Crayon-PK/Waste-Classification-Project/picture/IMG20260606160427.jpg

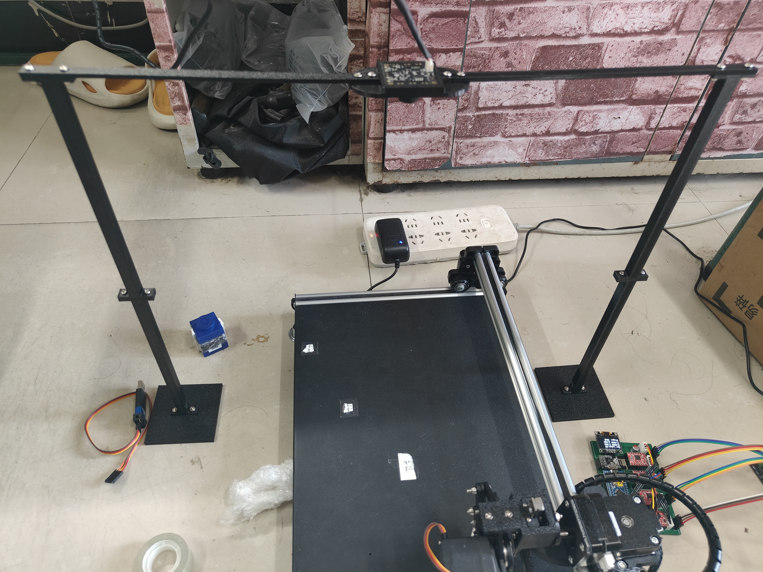
picture/IMG20260606160427.jpg
