Crayon-PK/Waste-Classification-Project/Firmware/BSP/Servo.c

#include "stm32f10x.h"                  // Device header

/**
  * 函    数：舵机初始化
  * 参    数：无
  * 返 回 值：无
  */
void Servo_Init(void)
{
	/* 开启时钟 */
	RCC_APB2PeriphClockCmd(RCC_APB2Periph_TIM1 | RCC_APB2Periph_GPIOA, ENABLE);

	/* GPIO初始化 */
	GPIO_InitTypeDef GPIO_InitStructure;
	GPIO_InitStructure.GPIO_Pin = GPIO_Pin_8;               // PA8
	GPIO_InitStructure.GPIO_Mode = GPIO_Mode_AF_PP;         // 复用推挽
	GPIO_InitStructure.GPIO_Speed = GPIO_Speed_50MHz;
	GPIO_Init(GPIOA, &GPIO_InitStructure);

	/* 时基单元初始化 */
	TIM_TimeBaseInitTypeDef TIM_TimeBaseInitStructure;
	TIM_TimeBaseInitStructure.TIM_Period = 20000 - 1;       // ARR
	TIM_TimeBaseInitStructure.TIM_Prescaler = 72 - 1;       // PSC
	TIM_TimeBaseInitStructure.TIM_ClockDivision = TIM_CKD_DIV1;
	TIM_TimeBaseInitStructure.TIM_CounterMode = TIM_CounterMode_Up;
	TIM_TimeBaseInitStructure.TIM_RepetitionCounter = 0;
	TIM_TimeBaseInit(TIM1, &TIM_TimeBaseInitStructure);

	/* 输出比较初始化 */
	TIM_OCInitTypeDef TIM_OCInitStructure;
	TIM_OCStructInit(&TIM_OCInitStructure);
	TIM_OCInitStructure.TIM_OCMode = TIM_OCMode_PWM1;
	TIM_OCInitStructure.TIM_OutputState = TIM_OutputState_Enable;
	TIM_OCInitStructure.TIM_OCPolarity = TIM_OCPolarity_High;
	TIM_OCInitStructure.TIM_Pulse = 0;                     // 初始CCR
	TIM_OC1Init(TIM1, &TIM_OCInitStructure);
	TIM_OC1PreloadConfig(TIM1, TIM_OCPreload_Enable);

	/* 使能 TIM1 输出PWM */
	TIM_CtrlPWMOutputs(TIM1, ENABLE);      // 高级定时器必须使能主输出
	TIM_Cmd(TIM1, ENABLE);
}

/**
  * 函    数：舵机设置角度
  * 参    数：Angle 要设置的舵机角度，范围：0~180
  * 返 回 值：无
  */
void Servo_SetAngle(float Angle)
{
	TIM_SetCompare1(TIM1,Angle / 180 * 2000 + 500);	//设置占空比
												//将角度线性变换，对应到舵机要求的占空比范围上
}
