Crayon-PK/Waste-Classification-Project/Firmware/BSP/NRF24L01.c

#include "stm32f10x.h"
#include "NRF24L01_Define.h"
#include <stddef.h>

/*---------------- 引脚定义 ----------------*/
#define NRF_CE   GPIO_Pin_1
#define NRF_CSN  GPIO_Pin_9
#define NRF_SCK  GPIO_Pin_10
#define NRF_MOSI GPIO_Pin_11
#define NRF_MISO GPIO_Pin_12
#define NRF_IRQ  GPIO_Pin_15

/*发送部分*/
uint8_t NRF24L01_TxAddress[5] = {0xAA, 0xBB, 0xCC, 0xDD, 0xEE};		//发送地址，固定5字节
#define NRF24L01_TX_PACKET_WIDTH		32							//发送数据包宽度，范围：1~32字节
uint8_t NRF24L01_TxPacket[NRF24L01_TX_PACKET_WIDTH];				//发送数据包

/*接收部分*/
uint8_t NRF24L01_RxAddress[5] = {0x11, 0x22, 0x33, 0x44, 0x55};		//接收通道0地址，固定5字节
#define NRF24L01_RX_PACKET_WIDTH		32							//接收通道0数据包宽度，范围：1~32字节
uint8_t NRF24L01_RxPacket[NRF24L01_RX_PACKET_WIDTH];				//接收数据包

typedef void (*NRF24L01_Callback_t)(uint8_t event);// event = 1: 接收完成, 2: 发送完成, 3: 达到最大重发次数
static NRF24L01_Callback_t driver_callback = NULL;

void NRF24L01_RegisterCallback(NRF24L01_Callback_t cb)
{ 
	driver_callback = cb;
}


void NRF24L01_W_CE(uint8_t BitValue){ GPIO_WriteBit(GPIOA, NRF_CE, (BitAction)BitValue); }
void NRF24L01_W_CSN(uint8_t BitValue){ GPIO_WriteBit(GPIOA, NRF_CSN, (BitAction)BitValue); }
void NRF24L01_W_SCK(uint8_t BitValue){ GPIO_WriteBit(GPIOA, NRF_SCK, (BitAction)BitValue); }
void NRF24L01_W_MOSI(uint8_t BitValue){ GPIO_WriteBit(GPIOA, NRF_MOSI, (BitAction)BitValue); }
uint8_t NRF24L01_R_MISO(void){ return GPIO_ReadInputDataBit(GPIOA, NRF_MISO); }

/**
  * 函    数：NRF24L01引脚初始化
  * 参    数：无
  * 返 回 值：无
  * 说    明：当上层函数需要初始化时，此函数会被调用
  *           用户需要将CSN、CE、MISO、SCK引脚初始化为推挽输出模式，MISO引脚初始化为上拉输入模式
  */
void NRF24L01_GPIO_Init(void)
{
	/*开启GPIO时钟*/
	RCC_APB2PeriphClockCmd(RCC_APB2Periph_GPIOA, ENABLE);
	GPIO_InitTypeDef GPIO_InitStructure;

	/* CE, CSN, SCK, MOSI 输出 */
	GPIO_InitStructure.GPIO_Mode = GPIO_Mode_Out_PP;
	GPIO_InitStructure.GPIO_Pin = NRF_CE | NRF_CSN | NRF_SCK | NRF_MOSI;
	GPIO_InitStructure.GPIO_Speed = GPIO_Speed_50MHz;
	GPIO_Init(GPIOA, &GPIO_InitStructure);

	/* MISO 输入上拉 */
	GPIO_InitStructure.GPIO_Mode = GPIO_Mode_IPU;
	GPIO_InitStructure.GPIO_Pin = NRF_MISO;
	GPIO_Init(GPIOA, &GPIO_InitStructure);
	
	/*置引脚初始化后的默认电平*/
	NRF24L01_W_CE(0);		//CE默认为0，退出收发模式
	NRF24L01_W_CSN(1);		//CSN默认为1，不选中从机
	NRF24L01_W_SCK(0);		//SCK默认为0，对应SPI模式0
	NRF24L01_W_MOSI(0);		//MOSI默认电平随意，1和0均可
}

void NRF24L01_IRQ_Init(void)
{
	GPIO_InitTypeDef GPIO_InitStructure;
	EXTI_InitTypeDef EXTI_InitStructure;
	NVIC_InitTypeDef NVIC_InitStructure;

	// 配置 PA15 为输入上拉
	RCC_APB2PeriphClockCmd(RCC_APB2Periph_GPIOA, ENABLE);
	GPIO_InitStructure.GPIO_Pin = NRF_IRQ;
	GPIO_InitStructure.GPIO_Mode = GPIO_Mode_IPU;  // 上拉输入
	GPIO_Init(GPIOA, &GPIO_InitStructure);

	// 配置外部中断线
	RCC_APB2PeriphClockCmd(RCC_APB2Periph_AFIO, ENABLE);
	GPIO_EXTILineConfig(GPIO_PortSourceGPIOA, GPIO_PinSource15);

	EXTI_InitStructure.EXTI_Line = EXTI_Line15;
	EXTI_InitStructure.EXTI_Mode = EXTI_Mode_Interrupt;
	EXTI_InitStructure.EXTI_Trigger = EXTI_Trigger_Falling;  // IRQ 低电平触发
	EXTI_InitStructure.EXTI_LineCmd = ENABLE;
	EXTI_Init(&EXTI_InitStructure);

	// 配置中断优先级
	NVIC_InitStructure.NVIC_IRQChannel = EXTI15_10_IRQn;
	NVIC_InitStructure.NVIC_IRQChannelPreemptionPriority = 11;
	NVIC_InitStructure.NVIC_IRQChannelSubPriority = 0;
	NVIC_InitStructure.NVIC_IRQChannelCmd = ENABLE;
	NVIC_Init(&NVIC_InitStructure);
}

/*********************引脚配置*/


/*通信协议*********************/

/**
  * 函    数：SPI交换一个字节
  * 参    数：Byte 要发送的一个字节数据，范围：0x00~0xFF
  * 返 回 值：接收得到的一个字节数据，范围：0x00~0xFF
  */
uint8_t NRF24L01_SPI_SwapByte(uint8_t Byte)
{
    uint8_t i;
    for (i = 0; i < 8; i++)
    {
        if (Byte & 0x80) NRF24L01_W_MOSI(1);
        else NRF24L01_W_MOSI(0);
        Byte <<= 1;
        NRF24L01_W_SCK(1);
        if (NRF24L01_R_MISO()) Byte |= 0x01;
        NRF24L01_W_SCK(0);
    }
    return Byte;
}

/*********************通信协议*/


/*指令实现*********************/

/**
  * 函    数：NRF24L01读取寄存器（一个字节）
  * 参    数：RegAddress 指定寄存器地址，范围：0x00~0x1F
  * 返 回 值：指定寄存器的数据，范围：0x00~0xFF
  */
uint8_t NRF24L01_ReadReg(uint8_t RegAddress)
{
    uint8_t Data;
    NRF24L01_W_CSN(0);
    NRF24L01_SPI_SwapByte(NRF24L01_R_REGISTER | RegAddress);
    Data = NRF24L01_SPI_SwapByte(NRF24L01_NOP);
    NRF24L01_W_CSN(1);
    return Data;
}

/**
  * 函    数：NRF24L01读取寄存器（多个字节）
  * 参    数：RegAddress 指定寄存器的地址，范围：0x00~0x1F
  * 参    数：DataArray 读取得到的数据数组，输出参数
  * 参    数：Count 指定读取的数量，范围：0~5
  * 返 回 值：无
  */
void NRF24L01_ReadRegs(uint8_t RegAddress, uint8_t *DataArray, uint8_t Count)
{
    uint8_t i;
    NRF24L01_W_CSN(0);
    NRF24L01_SPI_SwapByte(NRF24L01_R_REGISTER | RegAddress);
    for (i = 0; i < Count; i++) DataArray[i] = NRF24L01_SPI_SwapByte(NRF24L01_NOP);
    NRF24L01_W_CSN(1);
}

/**
  * 函    数：NRF24L01写入寄存器（一个字节）
  * 参    数：RegAddress 指定寄存器地址，范围：0x00~0x1F
  * 参    数：Data 要写入的一个字节数据，范围：0x00~0xFF
  * 返 回 值：无
  */
void NRF24L01_WriteReg(uint8_t RegAddress, uint8_t Data)
{
    NRF24L01_W_CSN(0);
    NRF24L01_SPI_SwapByte(NRF24L01_W_REGISTER | RegAddress);
    NRF24L01_SPI_SwapByte(Data);
    NRF24L01_W_CSN(1);
}

/**
  * 函    数：NRF24L01写入寄存器（多个字节）
  * 参    数：RegAddress 指定寄存器地址，范围：0x00~0x1F
  * 参    数：DataArray 要写入的数据数组，输入参数
  * 参    数：Count 指定写入的数量，范围：0~5
  * 返 回 值：无
  */
void NRF24L01_WriteRegs(uint8_t RegAddress, uint8_t *DataArray, uint8_t Count)
{
    uint8_t i;
    NRF24L01_W_CSN(0);
    NRF24L01_SPI_SwapByte(NRF24L01_W_REGISTER | RegAddress);
    for (i = 0; i < Count; i++) NRF24L01_SPI_SwapByte(DataArray[i]);
    NRF24L01_W_CSN(1);
}

/**
  * 函    数：NRF24L01读取Rx有效载荷
  * 参    数：DataArray 读取得到的数据数组，输出参数
  * 参    数：Count 指定读取的数量，范围：0~32
  * 返 回 值：无
  */
void NRF24L01_ReadRxPayload(uint8_t *DataArray, uint8_t Count)
{
    uint8_t i;
    NRF24L01_W_CSN(0);
    NRF24L01_SPI_SwapByte(NRF24L01_R_RX_PAYLOAD);
    for (i = 0; i < Count; i++) DataArray[i] = NRF24L01_SPI_SwapByte(NRF24L01_NOP);
    NRF24L01_W_CSN(1);
}


/**
  * 函    数：NRF24L01写入Tx有效载荷
  * 参    数：DataArray 要写入的数据数组，输入参数
  * 参    数：Count 指定写入的数量，范围：0~5
  * 返 回 值：无
  */
void NRF24L01_WriteTxPayload(uint8_t *DataArray, uint8_t Count)
{
    uint8_t i;
    NRF24L01_W_CSN(0);
    NRF24L01_SPI_SwapByte(NRF24L01_W_TX_PAYLOAD);
    for (i = 0; i < Count; i++) NRF24L01_SPI_SwapByte(DataArray[i]);
    NRF24L01_W_CSN(1);
}

/**
  * 函    数：NRF24L01清空Tx FIFO的所有数据
  * 参    数：无
  * 返 回 值：无
  */
void NRF24L01_FlushTx(void)
{
    NRF24L01_W_CSN(0);
    NRF24L01_SPI_SwapByte(NRF24L01_FLUSH_TX);
    NRF24L01_W_CSN(1);
}
/**
  * 函    数：NRF24L01清空Rx FIFO的所有数据
  * 参    数：无
  * 返 回 值：无
  */
void NRF24L01_FlushRx(void)
{
    NRF24L01_W_CSN(0);
    NRF24L01_SPI_SwapByte(NRF24L01_FLUSH_RX);
    NRF24L01_W_CSN(1);
}

/**
  * 函    数：NRF24L01读取状态寄存器
  * 参    数：无
  * 返 回 值：状态寄存器的值，范围：0x00~0xFF
  */
uint8_t NRF24L01_ReadStatus(void)
{
    uint8_t Status;
    NRF24L01_W_CSN(0);
    Status = NRF24L01_SPI_SwapByte(NRF24L01_NOP);
    NRF24L01_W_CSN(1);
    return Status;
}

/*********************指令实现*/


/*功能函数*********************/

/**
  * 函    数：NRF24L01进入掉电模式（CE = 0，PWR_UP = 0）
  * 参    数：无
  * 返 回 值：无
  */
void NRF24L01_PowerDown(void)
{
	uint8_t Config;
	
	/*CE置0，退出收发模式*/
	NRF24L01_W_CE(0);
	
	/*读-改-写操作流程，单独修改配置寄存器的某些位而不影响其他位*/
	Config = NRF24L01_ReadReg(NRF24L01_CONFIG);		//读取配置寄存器
	if (Config == 0xFF) {return;}					//配置寄存器全为1，出错，退出函数
	Config &= ~0x02;								//配置寄存器位1（PWR_UP）置0
	NRF24L01_WriteReg(NRF24L01_CONFIG, Config);		//写回配置寄存器
}

/**
  * 函    数：NRF24L01进入待机模式1（CE = 0，PWR_UP = 1）
  * 参    数：无
  * 返 回 值：无
  */
void NRF24L01_StandbyI(void)
{
	uint8_t Config;
	
	/*CE置0，退出收发模式*/
	NRF24L01_W_CE(0);
	
	/*读-改-写操作流程，单独修改配置寄存器的某些位而不影响其他位*/
	Config = NRF24L01_ReadReg(NRF24L01_CONFIG);		//读取配置寄存器
	if (Config == 0xFF) {return;}					//配置寄存器全为1，出错，退出函数
	Config |= 0x02;									//配置寄存器位1（PWR_UP）置1
	NRF24L01_WriteReg(NRF24L01_CONFIG, Config);		//写回配置寄存器
}

/**
  * 函    数：NRF24L01进入接收模式（CE = 1，PWR_UP = 1，PRIM_RX = 1）
  * 参    数：无
  * 返 回 值：无
  */
void NRF24L01_Rx(void)
{
	uint8_t Config;
	
	/*CE置0，退出收发模式*/
	NRF24L01_W_CE(0);
	
	/*读-改-写操作流程，单独修改配置寄存器的某些位而不影响其他位*/
	Config = NRF24L01_ReadReg(NRF24L01_CONFIG);		//读取配置寄存器
	if (Config == 0xFF) {return;}					//配置寄存器全为1，出错，退出函数
	Config |= 0x03;									//配置寄存器位1（PWR_UP）和位0（PRIM_RX）都置1
	NRF24L01_WriteReg(NRF24L01_CONFIG, Config);		//写回配置寄存器
	
	/*CE置1，进入收发模式，因为PRIM_RX为1，所以进入接收模式*/
	NRF24L01_W_CE(1);
}

/**
  * 函    数：NRF24L01进入发送模式（CE = 1，PWR_UP = 1，PRIM_RX = 0）
  * 参    数：无
  * 返 回 值：无
  */
void NRF24L01_Tx(void)
{
	uint8_t Config;
	
	/*CE置0，退出收发模式*/
	NRF24L01_W_CE(0);
	
	/*读-改-写操作流程，单独修改配置寄存器的某些位而不影响其他位*/
	Config = NRF24L01_ReadReg(NRF24L01_CONFIG);		//读取配置寄存器
	if (Config == 0xFF) {return;}					//配置寄存器全为1，出错，退出函数
	Config |= 0x02;									//配置寄存器位1（PWR_UP）置1
	Config &= ~0x01;								//配置寄存器位0（PRIM_RX）置0
	NRF24L01_WriteReg(NRF24L01_CONFIG, Config);		//写回配置寄存器
	
	/*CE置1，进入收发模式，因为PRIM_RX为0，所以进入发送模式*/
	NRF24L01_W_CE(1);
}

/**
  * 函    数：NRF24L01初始化
  * 参    数：无
  * 返 回 值：无
  * 说    明：使用前，需要调用此初始化函数
  */
void NRF24L01_Init(void)
{
	/*先调用底层的端口初始化*/
	NRF24L01_GPIO_Init();
	NRF24L01_IRQ_Init();
	/*初始化配置一系列寄存器，寄存器值的意义需参考手册中的寄存器描述*/
	/*以下配置通信双方必须保持一致，否则无法进行通信*/
	NRF24L01_WriteReg(NRF24L01_CONFIG, 0x0F);		// 配置基本工作模式的参数;PWR_UP,EN_CRC,16BIT_CRC,接收模式,开启所有中断
	NRF24L01_WriteReg(NRF24L01_EN_AA, 0x01);		// 使能通道0自动应答
	NRF24L01_WriteReg(NRF24L01_EN_RXADDR, 0x01);	//使能接收通道，只开启接收通道0
	NRF24L01_WriteReg(NRF24L01_SETUP_AW, 0x03);		//设置地址宽度，地址宽度为5字节
	NRF24L01_WriteReg(NRF24L01_SETUP_RETR, 0x1A);	//设置自动重发间隔时间:500us + 86us;最大自动重发次数:10次
	NRF24L01_WriteReg(NRF24L01_RF_CH, 0x00);		//设置RF通道为2.400GHz  频率=2.4+0GHz
	NRF24L01_WriteReg(NRF24L01_RF_SETUP, 0x0F);		//设置TX发射参数,0db增益,2Mbps,低噪声增益开启  
	
	/* 固定收发地址 */
	NRF24L01_WriteRegs(NRF24L01_TX_ADDR, NRF24L01_TxAddress, 5);    // 发送地址
	NRF24L01_WriteRegs(NRF24L01_RX_ADDR_P0, NRF24L01_RxAddress, 5); // 接收地址
	
	/* 接收通道0数据包宽度 */
	NRF24L01_WriteReg(NRF24L01_RX_PW_P0, NRF24L01_RX_PACKET_WIDTH);
	
	/*清空Tx FIFO的所有数据*/
	NRF24L01_FlushTx();
	
	/*清空Rx FIFO的所有数据*/
	NRF24L01_FlushRx();
	
	/*给状态寄存器的位4（MAX_RT）、位5（TX_DS）和位6（RX_DR）写1，清标志位*/
	NRF24L01_WriteReg(NRF24L01_STATUS, 0x70);
	
	/*初始化配置完成，芯片默认进入接收模式*/
	NRF24L01_Rx();
}

/**
  * 函    数：NRF24L01发送数据包
  * 参    数：无
  * 返 回 值：发送标志位，方便用户了解发送状态
  * 			1：发送成功，无错误
  * 			2：达到了最大重发次数仍未收到应答，可能是收发双方配置不一致、接收方不存在、接收FIFO已满或者多个发送数据包碰撞
  * 			3：状态寄存器的值不合法，可能是设备不存在、断路、短路或者引脚配置不正确
  * 			4：发送超时，可能是设备未初始化、断路、短路或者引脚配置不正确
  * 说    明：调用此函数前，直接修改全局数组NRF24L01_TxAddress和NRF24L01_TxPacket来设置发送的地址和数据
  */
uint8_t NRF24L01_Send(void)
{
	// 写发送有效载荷
	NRF24L01_WriteTxPayload(NRF24L01_TxPacket, NRF24L01_TX_PACKET_WIDTH);

	// 设置发送地址和接收应答地址
	NRF24L01_WriteRegs(NRF24L01_TX_ADDR, NRF24L01_TxAddress, 5);

	// 进入发送模式
	NRF24L01_Tx();
	return 0;
}

void EXTI15_10_IRQHandler(void)
{
    if(EXTI_GetITStatus(EXTI_Line15) != RESET)
    {
		uint8_t status = NRF24L01_ReadStatus();
	    if(driver_callback != NULL)
		{
			if (status & 0x40) driver_callback(1); /* RX_DR */
			if (status & 0x20) driver_callback(2); /* TX_DS */
			if (status & 0x10) driver_callback(3); /* MAX_RT */
		}
		EXTI_ClearITPendingBit(EXTI_Line15);
    }
}


/*********************功能函数*/


/*****************江协科技|版权所有****************/
/*****************jiangxiekeji.com*****************/
