Crayon-PK/Waste-Classification-Project/Firmware/BSP/OLED.c

/***************************************************************************************
  * 本程序由江协科技创建并免费开源共享
  * 你可以任意查看、使用和修改，并应用到自己的项目之中
  * 程序版权归江协科技所有，任何人或组织不得将其据为己有
  * 
  * 程序名称：				0.96寸OLED显示屏驱动程序（4针脚I2C接口）
  * 程序创建时间：			2023.10.24
  * 当前程序版本：			V1.2
  * 当前版本发布时间：		2024.4.24
  * 
  * 江协科技官方网站：		jiangxiekeji.com
  * 江协科技官方淘宝店：	jiangxiekeji.taobao.com
  * 程序介绍及更新动态：	jiangxiekeji.com/tutorial/oled.html
  * 
  * 如果你发现程序中的漏洞或者笔误，可通过邮件向我们反馈：feedback@jiangxiekeji.com
  * 发送邮件之前，你可以先到更新动态页面查看最新程序，如果此问题已经修改，则无需再发邮件
  ***************************************************************************************
  */

#include "stm32f10x.h"
#include "OLED.h"
#include <string.h>
#include <math.h>
#include <stdio.h>
#include <stdarg.h>
#include "Delay.h"

/**
  * 数据存储格式：
  * 纵向8点，高位在下，先从左到右，再从上到下
  * 每一个Bit对应一个像素点
  * 
  *      B0 B0                  B0 B0
  *      B1 B1                  B1 B1
  *      B2 B2                  B2 B2
  *      B3 B3  ------------->  B3 B3 --
  *      B4 B4                  B4 B4  |
  *      B5 B5                  B5 B5  |
  *      B6 B6                  B6 B6  |
  *      B7 B7                  B7 B7  |
  *                                    |
  *  -----------------------------------
  *  |   
  *  |   B0 B0                  B0 B0
  *  |   B1 B1                  B1 B1
  *  |   B2 B2                  B2 B2
  *  --> B3 B3  ------------->  B3 B3
  *      B4 B4                  B4 B4
  *      B5 B5                  B5 B5
  *      B6 B6                  B6 B6
  *      B7 B7                  B7 B7
  * 
  * 坐标轴定义：
  * 左上角为(0, 0)点
  * 横向向右为X轴，取值范围：0~127
  * 纵向向下为Y轴，取值范围：0~63
  * 
  *       0             X轴           127 
  *      .------------------------------->
  *    0 |
  *      |
  *      |
  *      |
  *  Y轴 |
  *      |
  *      |
  *      |
  *   63 |
  *      v
  * 
  */


/*全局变量*********************/

/**
  * OLED显存数组
  * 所有的显示函数，都只是对此显存数组进行读写
  * 随后调用OLED_Update函数或OLED_UpdateArea函数
  * 才会将显存数组的数据发送到OLED硬件，进行显示
  */
uint8_t OLED_DisplayBuf[8][128];

/*********************全局变量*/


/*引脚配置*********************/

void OLED_I2C_Init(void)
{
    GPIO_InitTypeDef GPIO_InitStructure;
    I2C_InitTypeDef  I2C_InitStructure;

    RCC_APB2PeriphClockCmd(RCC_APB2Periph_GPIOB, ENABLE);  // 使能GPIOB
    RCC_APB1PeriphClockCmd(RCC_APB1Periph_I2C1, ENABLE);   // 使能I2C1

    // 配置PB6 (SCL) 和 PB7 (SDA) 为复用开漏输出
    GPIO_InitStructure.GPIO_Pin = GPIO_Pin_6 | GPIO_Pin_7;
    GPIO_InitStructure.GPIO_Mode = GPIO_Mode_AF_OD;
    GPIO_InitStructure.GPIO_Speed = GPIO_Speed_50MHz;
    GPIO_Init(GPIOB, &GPIO_InitStructure);

    // I2C参数配置
    I2C_InitStructure.I2C_ClockSpeed = 400000;  // OLED支持400kHz
    I2C_InitStructure.I2C_Mode = I2C_Mode_I2C;
    I2C_InitStructure.I2C_DutyCycle = I2C_DutyCycle_2;
    I2C_InitStructure.I2C_OwnAddress1 = 0x00;
    I2C_InitStructure.I2C_Ack = I2C_Ack_Disable;
    I2C_InitStructure.I2C_AcknowledgedAddress = I2C_AcknowledgedAddress_7bit;

    I2C_Init(I2C1, &I2C_InitStructure);
    I2C_Cmd(I2C1, ENABLE);  // 使能I2C1
}

/**
  * 函    数：OLED写命令
  * 参    数：Command 要写入的命令值，范围：0x00~0xFF
  * 返 回 值：无
  */
void OLED_WriteCommand(uint8_t cmd)
{
    while (I2C_GetFlagStatus(I2C1, I2C_FLAG_BUSY));

    I2C_GenerateSTART(I2C1, ENABLE);
    while (!I2C_CheckEvent(I2C1, I2C_EVENT_MASTER_MODE_SELECT));

    I2C_Send7bitAddress(I2C1, 0x78, I2C_Direction_Transmitter);
    while (!I2C_CheckEvent(I2C1, I2C_EVENT_MASTER_TRANSMITTER_MODE_SELECTED));

    I2C_SendData(I2C1, 0x00);  // 控制字节：写命令
    while (!I2C_CheckEvent(I2C1, I2C_EVENT_MASTER_BYTE_TRANSMITTED));

    I2C_SendData(I2C1, cmd);  // 写入命令
    while (!I2C_CheckEvent(I2C1, I2C_EVENT_MASTER_BYTE_TRANSMITTED));

    I2C_GenerateSTOP(I2C1, ENABLE);
}

/**
  * 函    数：OLED写数据
  * 参    数：Data 要写入数据的起始地址
  * 参    数：Count 要写入数据的数量
  * 返 回 值：无
  */
void OLED_WriteData(uint8_t *data, uint8_t count)
{
    uint8_t i;

    while (I2C_GetFlagStatus(I2C1, I2C_FLAG_BUSY));

    I2C_GenerateSTART(I2C1, ENABLE);
    while (!I2C_CheckEvent(I2C1, I2C_EVENT_MASTER_MODE_SELECT));

    I2C_Send7bitAddress(I2C1, 0x78, I2C_Direction_Transmitter);
    while (!I2C_CheckEvent(I2C1, I2C_EVENT_MASTER_TRANSMITTER_MODE_SELECTED));

    I2C_SendData(I2C1, 0x40);  // 控制字节：写数据
    while (!I2C_CheckEvent(I2C1, I2C_EVENT_MASTER_BYTE_TRANSMITTED));

    for (i = 0; i < count; i++)
    {
        I2C_SendData(I2C1, data[i]);
        while (!I2C_CheckEvent(I2C1, I2C_EVENT_MASTER_BYTE_TRANSMITTED));
    }

    I2C_GenerateSTOP(I2C1, ENABLE);
}

/*********************通信协议*/


/*硬件配置*********************/

/**
  * 函    数：OLED初始化
  * 参    数：无
  * 返 回 值：无
  * 说    明：使用前，需要调用此初始化函数
  */
void OLED_Init(void)
{
	OLED_I2C_Init();			//先调用底层的端口初始化
	
	/*写入一系列的命令，对OLED进行初始化配置*/
	OLED_WriteCommand(0xAE);	//设置显示开启/关闭，0xAE关闭，0xAF开启
	
	OLED_WriteCommand(0xD5);	//设置显示时钟分频比/振荡器频率
	OLED_WriteCommand(0x80);	//0x00~0xFF
	
	OLED_WriteCommand(0xA8);	//设置多路复用率
	OLED_WriteCommand(0x3F);	//0x0E~0x3F
	
	OLED_WriteCommand(0xD3);	//设置显示偏移
	OLED_WriteCommand(0x00);	//0x00~0x7F
	
	OLED_WriteCommand(0x40);	//设置显示开始行，0x40~0x7F
	
	OLED_WriteCommand(0xA1);	//设置左右方向，0xA1正常，0xA0左右反置
	
	OLED_WriteCommand(0xC8);	//设置上下方向，0xC8正常，0xC0上下反置

	OLED_WriteCommand(0xDA);	//设置COM引脚硬件配置
	OLED_WriteCommand(0x12);
	
	OLED_WriteCommand(0x81);	//设置对比度
	OLED_WriteCommand(0xCF);	//0x00~0xFF

	OLED_WriteCommand(0xD9);	//设置预充电周期
	OLED_WriteCommand(0xF1);

	OLED_WriteCommand(0xDB);	//设置VCOMH取消选择级别
	OLED_WriteCommand(0x30);

	OLED_WriteCommand(0xA4);	//设置整个显示打开/关闭

	OLED_WriteCommand(0xA6);	//设置正常/反色显示，0xA6正常，0xA7反色

	OLED_WriteCommand(0x8D);	//设置充电泵
	OLED_WriteCommand(0x14);

	OLED_WriteCommand(0xAF);	//开启显示
	
	OLED_Clear();				//清空显存数组
	OLED_Update();				//更新显示，清屏，防止初始化后未显示内容时花屏
}

/**
  * 函    数：OLED设置显示光标位置
  * 参    数：Page 指定光标所在的页，范围：0~7
  * 参    数：X 指定光标所在的X轴坐标，范围：0~127
  * 返 回 值：无
  * 说    明：OLED默认的Y轴，只能8个Bit为一组写入，即1页等于8个Y轴坐标
  */
void OLED_SetCursor(uint8_t Page, uint8_t X)
{
	/*如果使用此程序驱动1.3寸的OLED显示屏，则需要解除此注释*/
	/*因为1.3寸的OLED驱动芯片（SH1106）有132列*/
	/*屏幕的起始列接在了第2列，而不是第0列*/
	/*所以需要将X加2，才能正常显示*/
//	X += 2;
	
	/*通过指令设置页地址和列地址*/
	OLED_WriteCommand(0xB0 | Page);					//设置页位置
	OLED_WriteCommand(0x10 | ((X & 0xF0) >> 4));	//设置X位置高4位
	OLED_WriteCommand(0x00 | (X & 0x0F));			//设置X位置低4位
}

/*********************硬件配置*/


/*工具函数*********************/

/*工具函数仅供内部部分函数使用*/

/**
  * 函    数：次方函数
  * 参    数：X 底数
  * 参    数：Y 指数
  * 返 回 值：等于X的Y次方
  */
uint32_t OLED_Pow(uint32_t X, uint32_t Y)
{
	uint32_t Result = 1;	//结果默认为1
	while (Y --)			//累乘Y次
	{
		Result *= X;		//每次把X累乘到结果上
	}
	return Result;
}

/**
  * 函    数：判断指定点是否在指定多边形内部
  * 参    数：nvert 多边形的顶点数
  * 参    数：vertx verty 包含多边形顶点的x和y坐标的数组
  * 参    数：testx testy 测试点的X和y坐标
  * 返 回 值：指定点是否在指定多边形内部，1：在内部，0：不在内部
  */
uint8_t OLED_pnpoly(uint8_t nvert, int16_t *vertx, int16_t *verty, int16_t testx, int16_t testy)
{
	int16_t i, j, c = 0;
	
	/*此算法由W. Randolph Franklin提出*/
	/*参考链接：https://wrfranklin.org/Research/Short_Notes/pnpoly.html*/
	for (i = 0, j = nvert - 1; i < nvert; j = i++)
	{
		if (((verty[i] > testy) != (verty[j] > testy)) &&
			(testx < (vertx[j] - vertx[i]) * (testy - verty[i]) / (verty[j] - verty[i]) + vertx[i]))
		{
			c = !c;
		}
	}
	return c;
}

/**
  * 函    数：判断指定点是否在指定角度内部
  * 参    数：X Y 指定点的坐标
  * 参    数：StartAngle EndAngle 起始角度和终止角度，范围：-180~180
  *           水平向右为0度，水平向左为180度或-180度，下方为正数，上方为负数，顺时针旋转
  * 返 回 值：指定点是否在指定角度内部，1：在内部，0：不在内部
  */
uint8_t OLED_IsInAngle(int16_t X, int16_t Y, int16_t StartAngle, int16_t EndAngle)
{
	int16_t PointAngle;
	PointAngle = atan2(Y, X) / 3.14 * 180;	//计算指定点的弧度，并转换为角度表示
	if (StartAngle < EndAngle)	//起始角度小于终止角度的情况
	{
		/*如果指定角度在起始终止角度之间，则判定指定点在指定角度*/
		if (PointAngle >= StartAngle && PointAngle <= EndAngle)
		{
			return 1;
		}
	}
	else			//起始角度大于于终止角度的情况
	{
		/*如果指定角度大于起始角度或者小于终止角度，则判定指定点在指定角度*/
		if (PointAngle >= StartAngle || PointAngle <= EndAngle)
		{
			return 1;
		}
	}
	return 0;		//不满足以上条件，则判断判定指定点不在指定角度
}

/*********************工具函数*/


/*功能函数*********************/

/**
  * 函    数：将OLED显存数组更新到OLED屏幕
  * 参    数：无
  * 返 回 值：无
  * 说    明：所有的显示函数，都只是对OLED显存数组进行读写
  *           随后调用OLED_Update函数或OLED_UpdateArea函数
  *           才会将显存数组的数据发送到OLED硬件，进行显示
  *           故调用显示函数后，要想真正地呈现在屏幕上，还需调用更新函数
  */
void OLED_Update(void)
{
	uint8_t j;
	/*遍历每一页*/
	for (j = 0; j < 8; j ++)
	{
		/*设置光标位置为每一页的第一列*/
		OLED_SetCursor(j, 0);
		/*连续写入128个数据，将显存数组的数据写入到OLED硬件*/
		OLED_WriteData(OLED_DisplayBuf[j], 128);
	}
}

/**
  * 函    数：将OLED显存数组部分更新到OLED屏幕
  * 参    数：X 指定区域左上角的横坐标，范围：-32768~32767，屏幕区域：0~127
  * 参    数：Y 指定区域左上角的纵坐标，范围：-32768~32767，屏幕区域：0~63
  * 参    数：Width 指定区域的宽度，范围：0~128
  * 参    数：Height 指定区域的高度，范围：0~64
  * 返 回 值：无
  * 说    明：此函数会至少更新参数指定的区域
  *           如果更新区域Y轴只包含部分页，则同一页的剩余部分会跟随一起更新
  * 说    明：所有的显示函数，都只是对OLED显存数组进行读写
  *           随后调用OLED_Update函数或OLED_UpdateArea函数
  *           才会将显存数组的数据发送到OLED硬件，进行显示
  *           故调用显示函数后，要想真正地呈现在屏幕上，还需调用更新函数
  */
void OLED_UpdateArea(int16_t X, int16_t Y, uint8_t Width, uint8_t Height)
{
	int16_t j;
	int16_t Page, Page1;
	
	/*负数坐标在计算页地址时需要加一个偏移*/
	/*(Y + Height - 1) / 8 + 1的目的是(Y + Height) / 8并向上取整*/
	Page = Y / 8;
	Page1 = (Y + Height - 1) / 8 + 1;
	if (Y < 0)
	{
		Page -= 1;
		Page1 -= 1;
	}
	
	/*遍历指定区域涉及的相关页*/
	for (j = Page; j < Page1; j ++)
	{
		if (X >= 0 && X <= 127 && j >= 0 && j <= 7)		//超出屏幕的内容不显示
		{
			/*设置光标位置为相关页的指定列*/
			OLED_SetCursor(j, X);
			/*连续写入Width个数据，将显存数组的数据写入到OLED硬件*/
			OLED_WriteData(&OLED_DisplayBuf[j][X], Width);
		}
	}
}

/**
  * 函    数：将OLED显存数组全部清零
  * 参    数：无
  * 返 回 值：无
  * 说    明：调用此函数后，要想真正地呈现在屏幕上，还需调用更新函数
  */
void OLED_Clear(void)
{
	uint8_t i, j;
	for (j = 0; j < 8; j ++)				//遍历8页
	{
		for (i = 0; i < 128; i ++)			//遍历128列
		{
			OLED_DisplayBuf[j][i] = 0x00;	//将显存数组数据全部清零
		}
	}
}

/**
  * 函    数：将OLED显存数组部分清零
  * 参    数：X 指定区域左上角的横坐标，范围：-32768~32767，屏幕区域：0~127
  * 参    数：Y 指定区域左上角的纵坐标，范围：-32768~32767，屏幕区域：0~63
  * 参    数：Width 指定区域的宽度，范围：0~128
  * 参    数：Height 指定区域的高度，范围：0~64
  * 返 回 值：无
  * 说    明：调用此函数后，要想真正地呈现在屏幕上，还需调用更新函数
  */
void OLED_ClearArea(int16_t X, int16_t Y, uint8_t Width, uint8_t Height)
{
	int16_t i, j;
	
	for (j = Y; j < Y + Height; j ++)		//遍历指定页
	{
		for (i = X; i < X + Width; i ++)	//遍历指定列
		{
			if (i >= 0 && i <= 127 && j >=0 && j <= 63)				//超出屏幕的内容不显示
			{
				OLED_DisplayBuf[j / 8][i] &= ~(0x01 << (j % 8));	//将显存数组指定数据清零
			}
		}
	}
}

/**
  * 函    数：将OLED显存数组全部取反
  * 参    数：无
  * 返 回 值：无
  * 说    明：调用此函数后，要想真正地呈现在屏幕上，还需调用更新函数
  */
void OLED_Reverse(void)
{
	uint8_t i, j;
	for (j = 0; j < 8; j ++)				//遍历8页
	{
		for (i = 0; i < 128; i ++)			//遍历128列
		{
			OLED_DisplayBuf[j][i] ^= 0xFF;	//将显存数组数据全部取反
		}
	}
}
	
/**
  * 函    数：将OLED显存数组部分取反
  * 参    数：X 指定区域左上角的横坐标，范围：-32768~32767，屏幕区域：0~127
  * 参    数：Y 指定区域左上角的纵坐标，范围：-32768~32767，屏幕区域：0~63
  * 参    数：Width 指定区域的宽度，范围：0~128
  * 参    数：Height 指定区域的高度，范围：0~64
  * 返 回 值：无
  * 说    明：调用此函数后，要想真正地呈现在屏幕上，还需调用更新函数
  */
void OLED_ReverseArea(int16_t X, int16_t Y, uint8_t Width, uint8_t Height)
{
	int16_t i, j;
	
	for (j = Y; j < Y + Height; j ++)		//遍历指定页
	{
		for (i = X; i < X + Width; i ++)	//遍历指定列
		{
			if (i >= 0 && i <= 127 && j >=0 && j <= 63)			//超出屏幕的内容不显示
			{
				OLED_DisplayBuf[j / 8][i] ^= 0x01 << (j % 8);	//将显存数组指定数据取反
			}
		}
	}
}

/**
  * 函    数：OLED显示一个字符
  * 参    数：X 指定字符左上角的横坐标，范围：-32768~32767，屏幕区域：0~127
  * 参    数：Y 指定字符左上角的纵坐标，范围：-32768~32767，屏幕区域：0~63
  * 参    数：Char 指定要显示的字符，范围：ASCII码可见字符
  * 参    数：FontSize 指定字体大小
  *           范围：OLED_8X16		宽8像素，高16像素
  *                 OLED_6X8		宽6像素，高8像素
  * 返 回 值：无
  * 说    明：调用此函数后，要想真正地呈现在屏幕上，还需调用更新函数
  */
void OLED_ShowChar(int16_t X, int16_t Y, char Char, uint8_t FontSize)
{
	if (FontSize == OLED_8X16)		//字体为宽8像素，高16像素
	{
		/*将ASCII字模库OLED_F8x16的指定数据以8*16的图像格式显示*/
		OLED_ShowImage(X, Y, 8, 16, OLED_F8x16[Char - ' ']);
	}
	else if(FontSize == OLED_6X8)	//字体为宽6像素，高8像素
	{
		/*将ASCII字模库OLED_F6x8的指定数据以6*8的图像格式显示*/
		OLED_ShowImage(X, Y, 6, 8, OLED_F6x8[Char - ' ']);
	}
}

/**
  * 函    数：OLED显示字符串
  * 参    数：X 指定字符串左上角的横坐标，范围：-32768~32767，屏幕区域：0~127
  * 参    数：Y 指定字符串左上角的纵坐标，范围：-32768~32767，屏幕区域：0~63
  * 参    数：String 指定要显示的字符串，范围：ASCII码可见字符组成的字符串
  * 参    数：FontSize 指定字体大小
  *           范围：OLED_8X16		宽8像素，高16像素
  *                 OLED_6X8		宽6像素，高8像素
  * 返 回 值：无
  * 说    明：调用此函数后，要想真正地呈现在屏幕上，还需调用更新函数
  */
void OLED_ShowString(int16_t X, int16_t Y, char *String, uint8_t FontSize)
{
	uint8_t i;
	for (i = 0; String[i] != '\0'; i++)		//遍历字符串的每个字符
	{
		/*调用OLED_ShowChar函数，依次显示每个字符*/
		OLED_ShowChar(X + i * FontSize, Y, String[i], FontSize);
	}
}

/**
  * 函    数：OLED显示数字（十进制，正整数）
  * 参    数：X 指定数字左上角的横坐标，范围：-32768~32767，屏幕区域：0~127
  * 参    数：Y 指定数字左上角的纵坐标，范围：-32768~32767，屏幕区域：0~63
  * 参    数：Number 指定要显示的数字，范围：0~4294967295
  * 参    数：Length 指定数字的长度，范围：0~10
  * 参    数：FontSize 指定字体大小
  *           范围：OLED_8X16		宽8像素，高16像素
  *                 OLED_6X8		宽6像素，高8像素
  * 返 回 值：无
  * 说    明：调用此函数后，要想真正地呈现在屏幕上，还需调用更新函数
  */
void OLED_ShowNum(int16_t X, int16_t Y, uint32_t Number, uint8_t Length, uint8_t FontSize)
{
	uint8_t i;
	for (i = 0; i < Length; i++)		//遍历数字的每一位							
	{
		/*调用OLED_ShowChar函数，依次显示每个数字*/
		/*Number / OLED_Pow(10, Length - i - 1) % 10 可以十进制提取数字的每一位*/
		/*+ '0' 可将数字转换为字符格式*/
		OLED_ShowChar(X + i * FontSize, Y, Number / OLED_Pow(10, Length - i - 1) % 10 + '0', FontSize);
	}
}

/**
  * 函    数：OLED显示有符号数字（十进制，整数）
  * 参    数：X 指定数字左上角的横坐标，范围：-32768~32767，屏幕区域：0~127
  * 参    数：Y 指定数字左上角的纵坐标，范围：-32768~32767，屏幕区域：0~63
  * 参    数：Number 指定要显示的数字，范围：-2147483648~2147483647
  * 参    数：Length 指定数字的长度，范围：0~10
  * 参    数：FontSize 指定字体大小
  *           范围：OLED_8X16		宽8像素，高16像素
  *                 OLED_6X8		宽6像素，高8像素
  * 返 回 值：无
  * 说    明：调用此函数后，要想真正地呈现在屏幕上，还需调用更新函数
  */
void OLED_ShowSignedNum(int16_t X, int16_t Y, int32_t Number, uint8_t Length, uint8_t FontSize)
{
	uint8_t i;
	uint32_t Number1;
	
	if (Number >= 0)						//数字大于等于0
	{
		OLED_ShowChar(X, Y, '+', FontSize);	//显示+号
		Number1 = Number;					//Number1直接等于Number
	}
	else									//数字小于0
	{
		OLED_ShowChar(X, Y, '-', FontSize);	//显示-号
		Number1 = -Number;					//Number1等于Number取负
	}
	
	for (i = 0; i < Length; i++)			//遍历数字的每一位								
	{
		/*调用OLED_ShowChar函数，依次显示每个数字*/
		/*Number1 / OLED_Pow(10, Length - i - 1) % 10 可以十进制提取数字的每一位*/
		/*+ '0' 可将数字转换为字符格式*/
		OLED_ShowChar(X + (i + 1) * FontSize, Y, Number1 / OLED_Pow(10, Length - i - 1) % 10 + '0', FontSize);
	}
}

/**
  * 函    数：OLED显示十六进制数字（十六进制，正整数）
  * 参    数：X 指定数字左上角的横坐标，范围：-32768~32767，屏幕区域：0~127
  * 参    数：Y 指定数字左上角的纵坐标，范围：-32768~32767，屏幕区域：0~63
  * 参    数：Number 指定要显示的数字，范围：0x00000000~0xFFFFFFFF
  * 参    数：Length 指定数字的长度，范围：0~8
  * 参    数：FontSize 指定字体大小
  *           范围：OLED_8X16		宽8像素，高16像素
  *                 OLED_6X8		宽6像素，高8像素
  * 返 回 值：无
  * 说    明：调用此函数后，要想真正地呈现在屏幕上，还需调用更新函数
  */
void OLED_ShowHexNum(int16_t X, int16_t Y, uint32_t Number, uint8_t Length, uint8_t FontSize)
{
	uint8_t i, SingleNumber;
	for (i = 0; i < Length; i++)		//遍历数字的每一位
	{
		/*以十六进制提取数字的每一位*/
		SingleNumber = Number / OLED_Pow(16, Length - i - 1) % 16;
		
		if (SingleNumber < 10)			//单个数字小于10
		{
			/*调用OLED_ShowChar函数，显示此数字*/
			/*+ '0' 可将数字转换为字符格式*/
			OLED_ShowChar(X + i * FontSize, Y, SingleNumber + '0', FontSize);
		}
		else							//单个数字大于10
		{
			/*调用OLED_ShowChar函数，显示此数字*/
			/*+ 'A' 可将数字转换为从A开始的十六进制字符*/
			OLED_ShowChar(X + i * FontSize, Y, SingleNumber - 10 + 'A', FontSize);
		}
	}
}

/**
  * 函    数：OLED显示二进制数字（二进制，正整数）
  * 参    数：X 指定数字左上角的横坐标，范围：-32768~32767，屏幕区域：0~127
  * 参    数：Y 指定数字左上角的纵坐标，范围：-32768~32767，屏幕区域：0~63
  * 参    数：Number 指定要显示的数字，范围：0x00000000~0xFFFFFFFF
  * 参    数：Length 指定数字的长度，范围：0~16
  * 参    数：FontSize 指定字体大小
  *           范围：OLED_8X16		宽8像素，高16像素
  *                 OLED_6X8		宽6像素，高8像素
  * 返 回 值：无
  * 说    明：调用此函数后，要想真正地呈现在屏幕上，还需调用更新函数
  */
void OLED_ShowBinNum(int16_t X, int16_t Y, uint32_t Number, uint8_t Length, uint8_t FontSize)
{
	uint8_t i;
	for (i = 0; i < Length; i++)		//遍历数字的每一位	
	{
		/*调用OLED_ShowChar函数，依次显示每个数字*/
		/*Number / OLED_Pow(2, Length - i - 1) % 2 可以二进制提取数字的每一位*/
		/*+ '0' 可将数字转换为字符格式*/
		OLED_ShowChar(X + i * FontSize, Y, Number / OLED_Pow(2, Length - i - 1) % 2 + '0', FontSize);
	}
}

/**
  * 函    数：OLED显示浮点数字（十进制，小数）
  * 参    数：X 指定数字左上角的横坐标，范围：-32768~32767，屏幕区域：0~127
  * 参    数：Y 指定数字左上角的纵坐标，范围：-32768~32767，屏幕区域：0~63
  * 参    数：Number 指定要显示的数字，范围：-4294967295.0~4294967295.0
  * 参    数：IntLength 指定数字的整数位长度，范围：0~10
  * 参    数：FraLength 指定数字的小数位长度，范围：0~9，小数进行四舍五入显示
  * 参    数：FontSize 指定字体大小
  *           范围：OLED_8X16		宽8像素，高16像素
  *                 OLED_6X8		宽6像素，高8像素
  * 返 回 值：无
  * 说    明：调用此函数后，要想真正地呈现在屏幕上，还需调用更新函数
  */
void OLED_ShowFloatNum(int16_t X, int16_t Y, double Number, uint8_t IntLength, uint8_t FraLength, uint8_t FontSize)
{
	uint32_t PowNum, IntNum, FraNum;
	
	if (Number >= 0)						//数字大于等于0
	{
		OLED_ShowChar(X, Y, '+', FontSize);	//显示+号
	}
	else									//数字小于0
	{
		OLED_ShowChar(X, Y, '-', FontSize);	//显示-号
		Number = -Number;					//Number取负
	}
	
	/*提取整数部分和小数部分*/
	IntNum = Number;						//直接赋值给整型变量，提取整数
	Number -= IntNum;						//将Number的整数减掉，防止之后将小数乘到整数时因数过大造成错误
	PowNum = OLED_Pow(10, FraLength);		//根据指定小数的位数，确定乘数
	FraNum = round(Number * PowNum);		//将小数乘到整数，同时四舍五入，避免显示误差
	IntNum += FraNum / PowNum;				//若四舍五入造成了进位，则需要再加给整数
	
	/*显示整数部分*/
	OLED_ShowNum(X + FontSize, Y, IntNum, IntLength, FontSize);
	
	/*显示小数点*/
	OLED_ShowChar(X + (IntLength + 1) * FontSize, Y, '.', FontSize);
	
	/*显示小数部分*/
	OLED_ShowNum(X + (IntLength + 2) * FontSize, Y, FraNum, FraLength, FontSize);
}

/**
  * 函    数：OLED显示图像
  * 参    数：X 指定图像左上角的横坐标，范围：-32768~32767，屏幕区域：0~127
  * 参    数：Y 指定图像左上角的纵坐标，范围：-32768~32767，屏幕区域：0~63
  * 参    数：Width 指定图像的宽度，范围：0~128
  * 参    数：Height 指定图像的高度，范围：0~64
  * 参    数：Image 指定要显示的图像
  * 返 回 值：无
  * 说    明：调用此函数后，要想真正地呈现在屏幕上，还需调用更新函数
  */
void OLED_ShowImage(int16_t X, int16_t Y, uint8_t Width, uint8_t Height, const uint8_t *Image)//---------------------------------------------------------
{
	uint8_t i = 0, j = 0;
	int16_t Page, Shift;
	
	/*将图像所在区域清空*/
	OLED_ClearArea(X, Y, Width, Height);
	
	/*遍历指定图像涉及的相关页*/
	/*(Height - 1) / 8 + 1的目的是Height / 8并向上取整*/
	for (j = 0; j < (Height - 1) / 8 + 1; j ++)
	{
		/*遍历指定图像涉及的相关列*/
		for (i = 0; i < Width; i ++)
		{
			if (X + i >= 0 && X + i <= 127)		//超出屏幕的内容不显示
			{
				/*负数坐标在计算页地址和移位时需要加一个偏移*/
				Page = Y / 8;
				Shift = Y % 8;
				if (Y < 0)
				{
					Page -= 1;
					Shift += 8;
				}
				
				if (Page + j >= 0 && Page + j <= 7)		//超出屏幕的内容不显示
				{
					/*显示图像在当前页的内容*/
					OLED_DisplayBuf[Page + j][X + i] |= Image[j * Width + i] << (Shift);
				}
				
				if (Page + j + 1 >= 0 && Page + j + 1 <= 7)		//超出屏幕的内容不显示
				{					
					/*显示图像在下一页的内容*/
					OLED_DisplayBuf[Page + j + 1][X + i] |= Image[j * Width + i] >> (8 - Shift);
				}
			}
		}
	}
}


/*****************江协科技|版权所有****************/
/*****************jiangxiekeji.com*****************/
