Crayon-PK/Waste-Classification-Project/Firmware/BSP/OLED_Data.h

#ifndef __OLED_DATA_H
#define __OLED_DATA_H

#include <stdint.h>

/*ASCII字模数据声明*/

extern const uint8_t OLED_F8x16[][16];
extern const uint8_t OLED_F6x8[][6];

/*图像数据声明*/
extern const uint8_t Diode[][128];
/*按照上面的格式，在这个位置加入新的图像数据声明*/
//...

#endif


/*****************江协科技|版权所有****************/
/*****************jiangxiekeji.com*****************/
